legeonaf/robotics.ellak/images/iHome.jpg

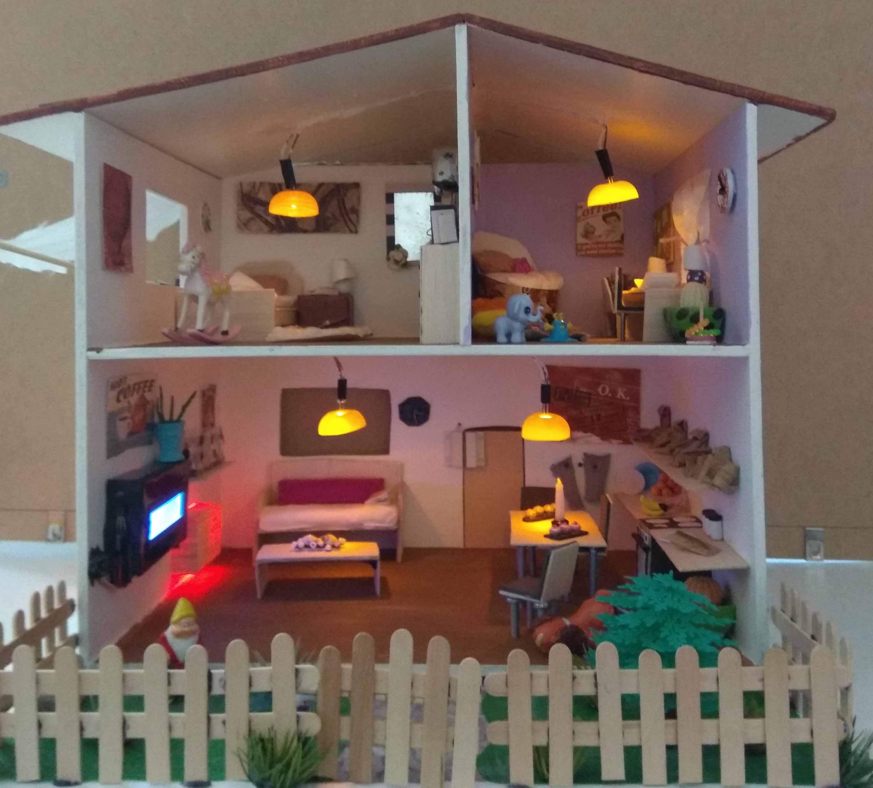
images/iHome.jpg
