legeonaf/robotics.ellak/photos/_MG_0073_resize.jpg

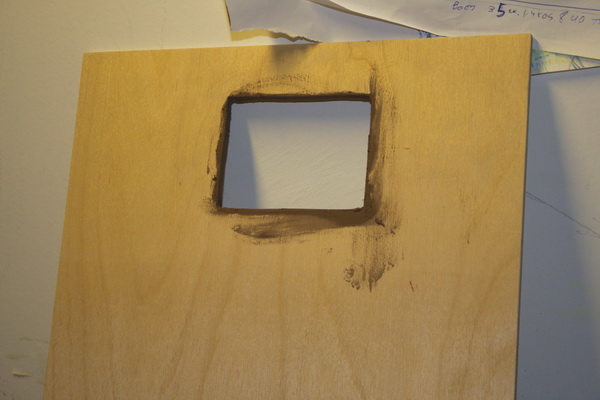
photos/_MG_0073_resize.jpg
