legeonaf/robotics.ellak/photos/_MG_0074_resize.jpg

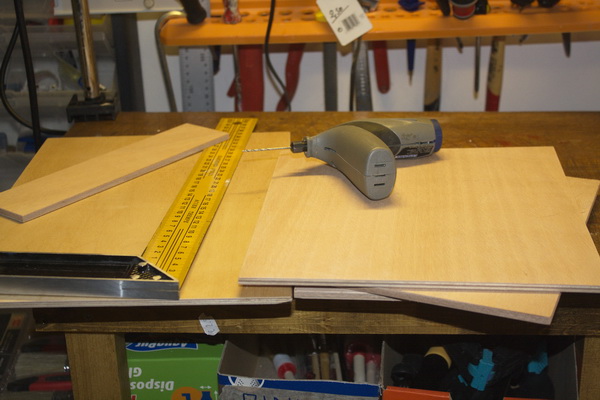
photos/_MG_0074_resize.jpg
