legeonaf/robotics.ellak/photos/_MG_0078_resize.jpg

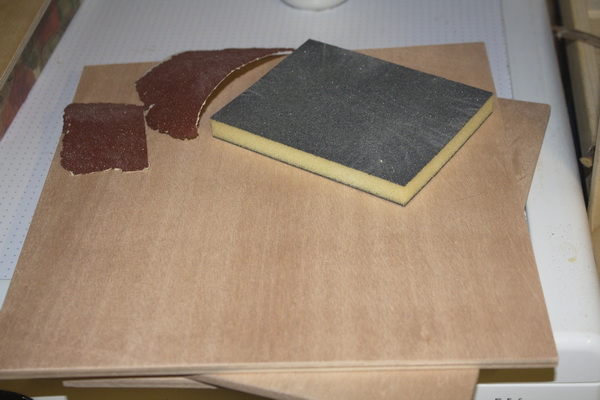
photos/_MG_0078_resize.jpg
