legeonaf/robotics.ellak/photos/_MG_0083_resize.jpg

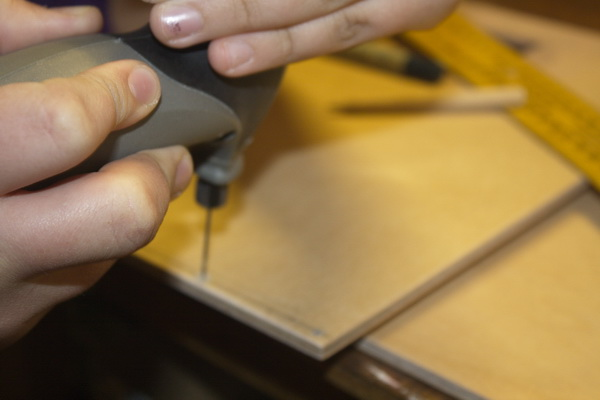
photos/_MG_0083_resize.jpg
