legeonaf/robotics.ellak/photos/_MG_0085_resize.jpg

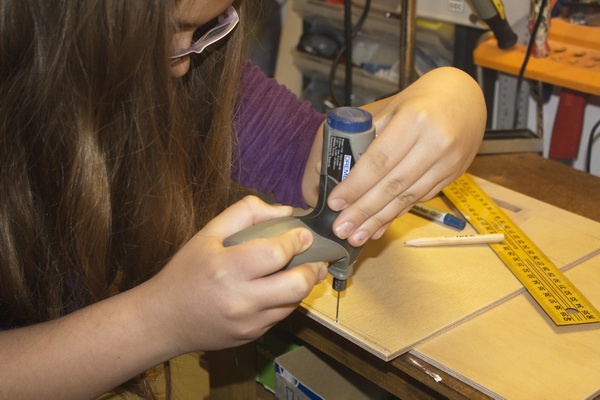
photos/_MG_0085_resize.jpg
