legeonaf/robotics.ellak/photos/_MG_0087_resize.jpg

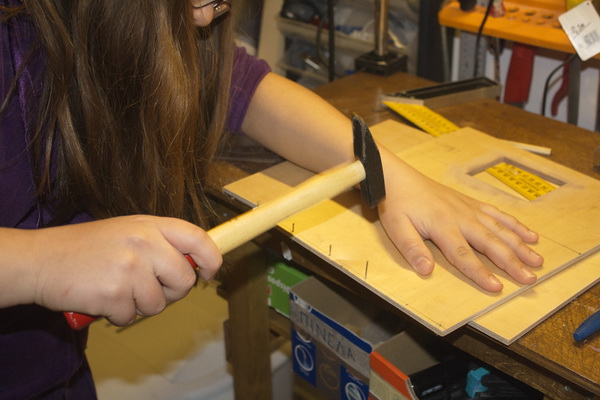
photos/_MG_0087_resize.jpg
