legeonaf/robotics.ellak/photos/_MG_0088_resize.jpg

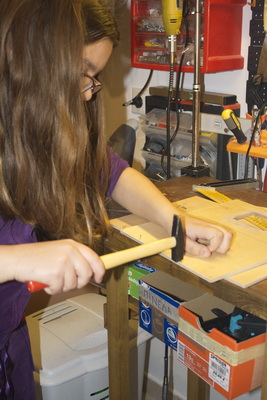
photos/_MG_0088_resize.jpg
