legeonaf/robotics.ellak/photos/_MG_0089_resize.jpg

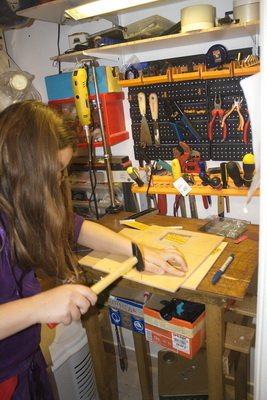
photos/_MG_0089_resize.jpg
