legeonaf/robotics.ellak/photos/_MG_0090_resize.jpg

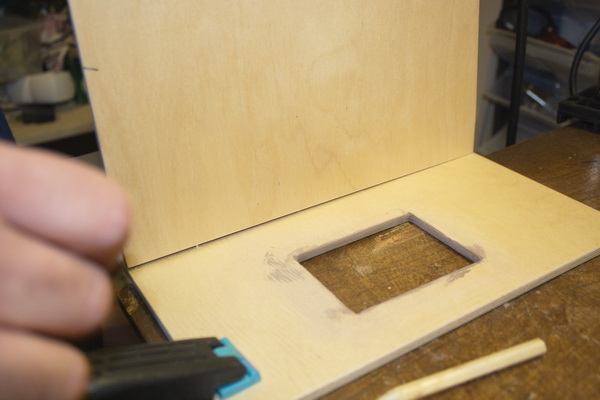
photos/_MG_0090_resize.jpg
