legeonaf/robotics.ellak/photos/_MG_0091_resize.jpg

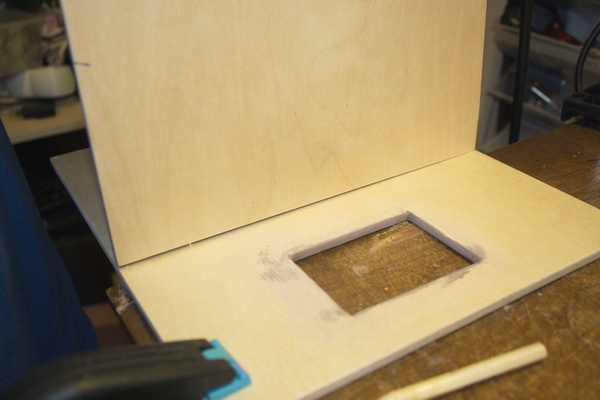
photos/_MG_0091_resize.jpg
