legeonaf/robotics.ellak/photos/_MG_0105_resize.jpg

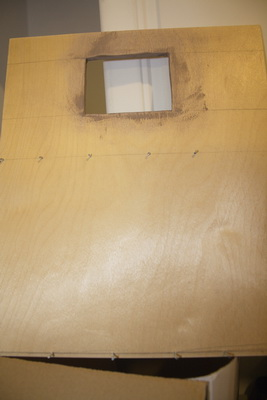
photos/_MG_0105_resize.jpg
