legeonaf/robotics.ellak/photos/_MG_0110_resize.jpg

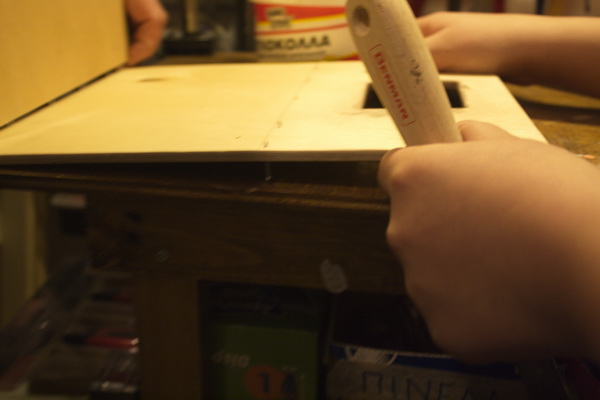
photos/_MG_0110_resize.jpg
