legeonaf/robotics.ellak/photos/_MG_0133_resize.jpg

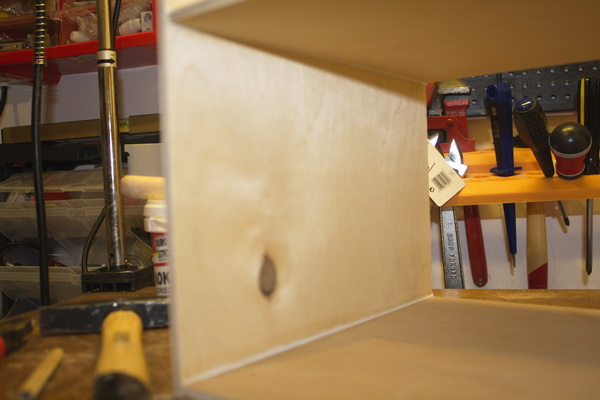
photos/_MG_0133_resize.jpg
