legeonaf/robotics.ellak/photos/_MG_0134_resize.jpg

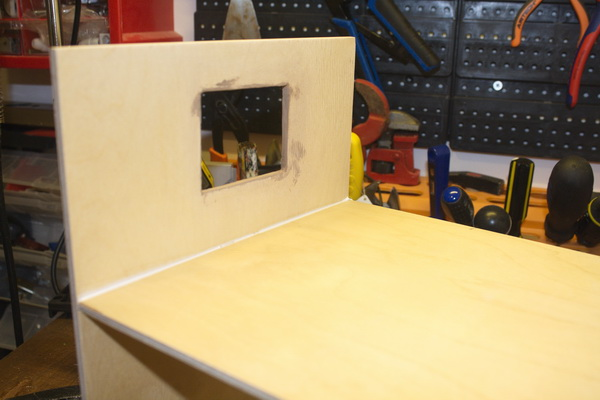
photos/_MG_0134_resize.jpg
