legeonaf/robotics.ellak/photos/_MG_0135_resize.jpg

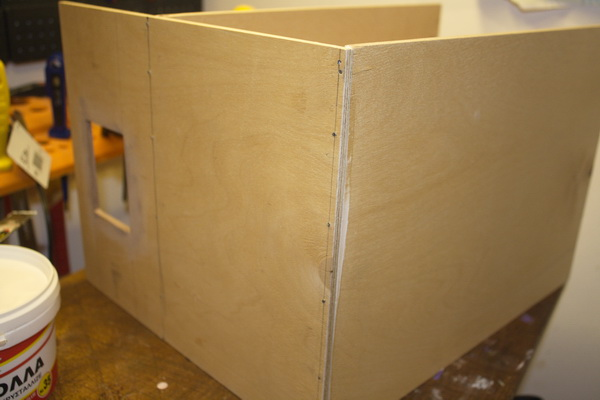
photos/_MG_0135_resize.jpg
