legeonaf/robotics.ellak/photos/_MG_0138_resize.jpg

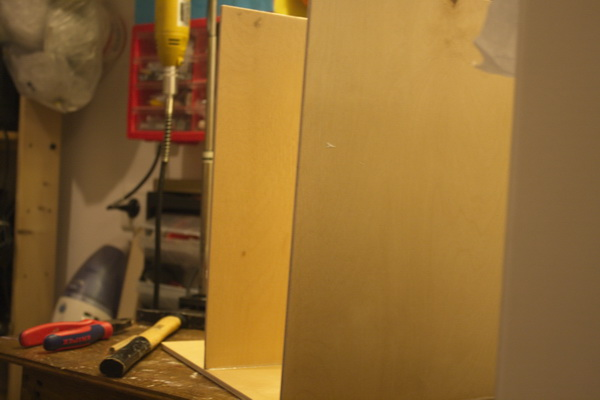
photos/_MG_0138_resize.jpg
