legeonaf/robotics.ellak/photos/_MG_0139_resize.jpg

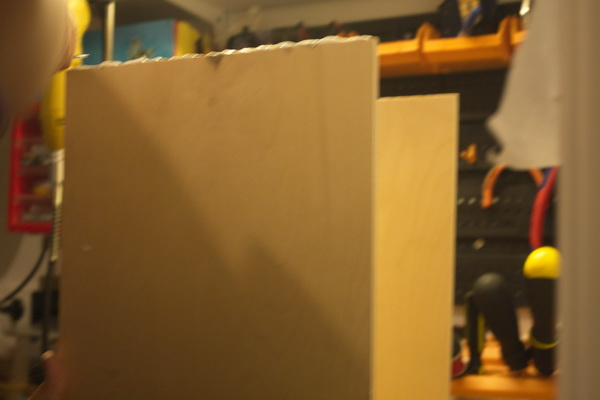
photos/_MG_0139_resize.jpg
