legeonaf/robotics.ellak/photos/_MG_0140_resize.jpg

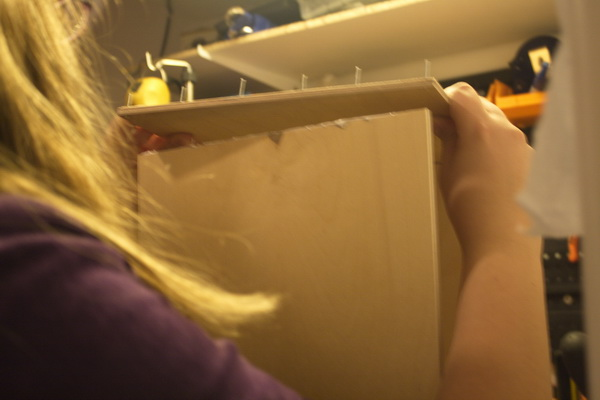
photos/_MG_0140_resize.jpg
