legeonaf/robotics.ellak/photos/_MG_0141_resize.jpg

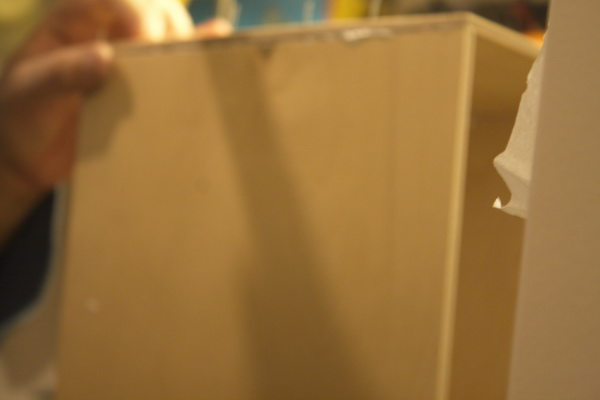
photos/_MG_0141_resize.jpg
