legeonaf/robotics.ellak/photos/_MG_0144_resize.jpg

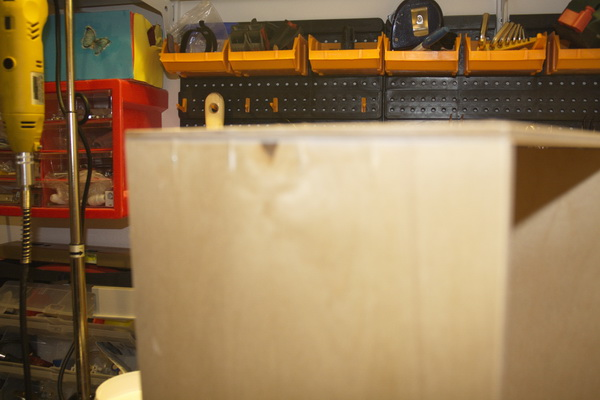
photos/_MG_0144_resize.jpg
