legeonaf/robotics.ellak/photos/_MG_0145_resize.jpg

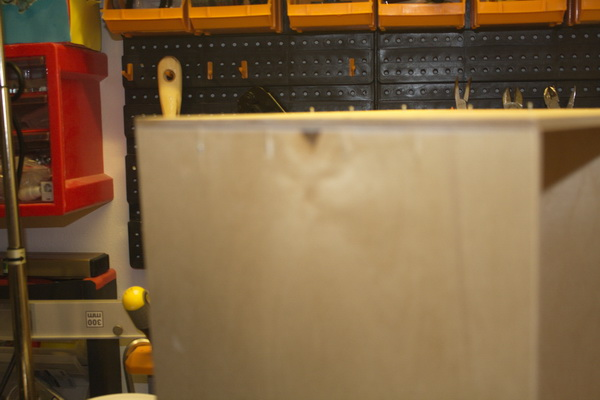
photos/_MG_0145_resize.jpg
