legeonaf/robotics.ellak/photos/_MG_0146_resize.jpg

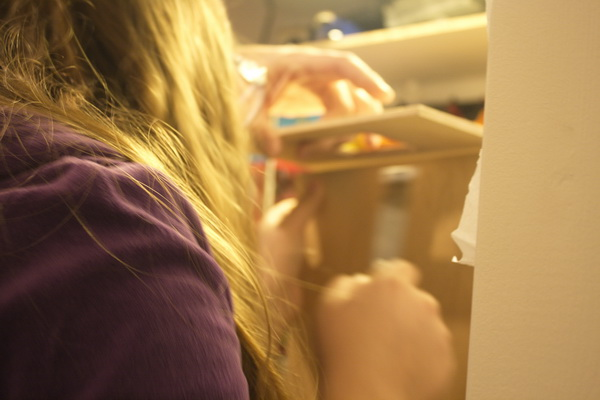
photos/_MG_0146_resize.jpg
