legeonaf/robotics.ellak/photos/_MG_0149_resize.jpg

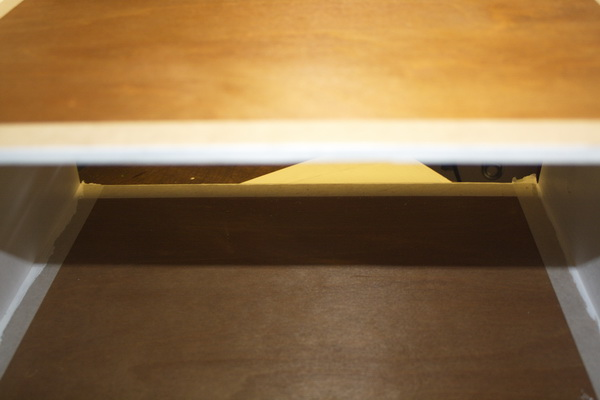
photos/_MG_0149_resize.jpg
