legeonaf/robotics.ellak/photos/_MG_0150_resize.jpg

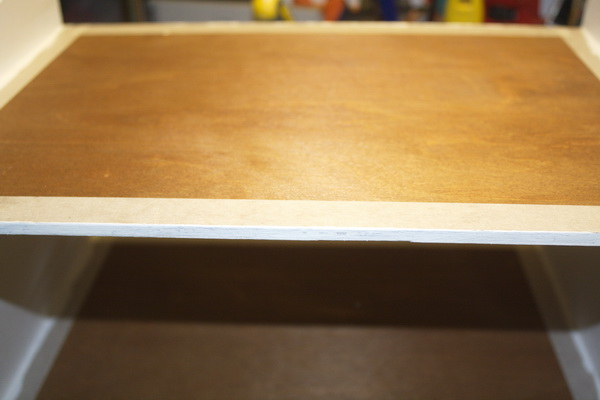
photos/_MG_0150_resize.jpg
