legeonaf/robotics.ellak/photos/_MG_0152_resize.jpg

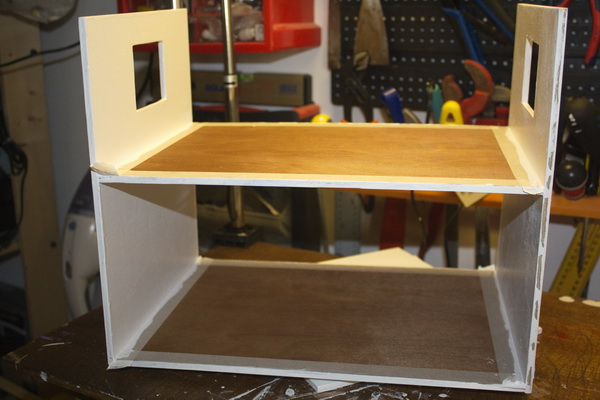
photos/_MG_0152_resize.jpg
