legeonaf/robotics.ellak/photos/_MG_0153_resize.jpg

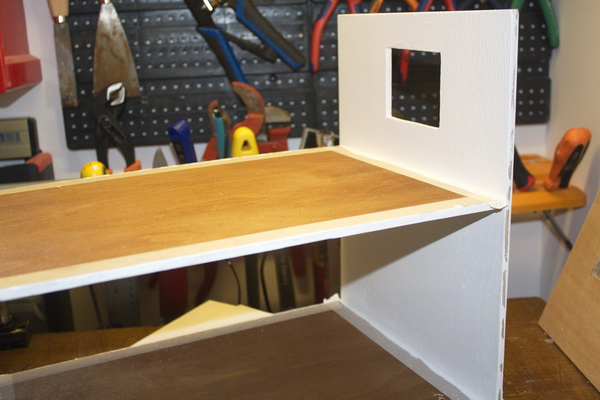
photos/_MG_0153_resize.jpg
