legeonaf/robotics.ellak/photos/_MG_0154_resize.jpg

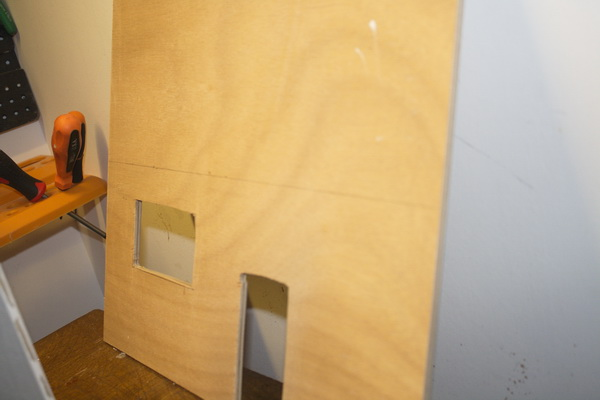
photos/_MG_0154_resize.jpg
