legeonaf/robotics.ellak/photos/_MG_0155_resize.jpg

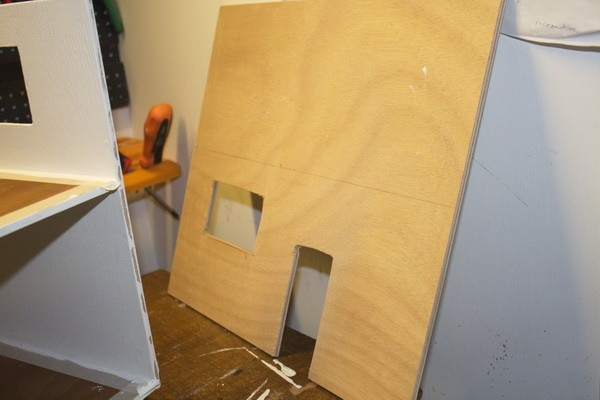
photos/_MG_0155_resize.jpg
