legeonaf/robotics.ellak/photos/_MG_0157_resize.jpg

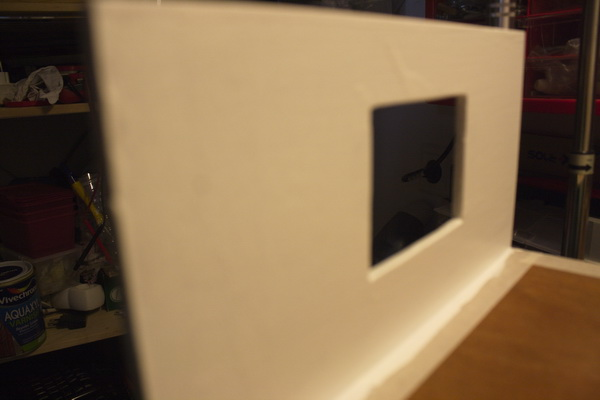
photos/_MG_0157_resize.jpg
