legeonaf/robotics.ellak/photos/_MG_0168_resize.jpg

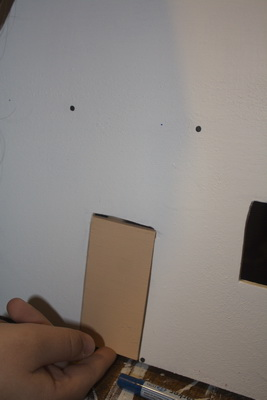
photos/_MG_0168_resize.jpg
