legeonaf/robotics.ellak/photos/_MG_0169_resize.jpg

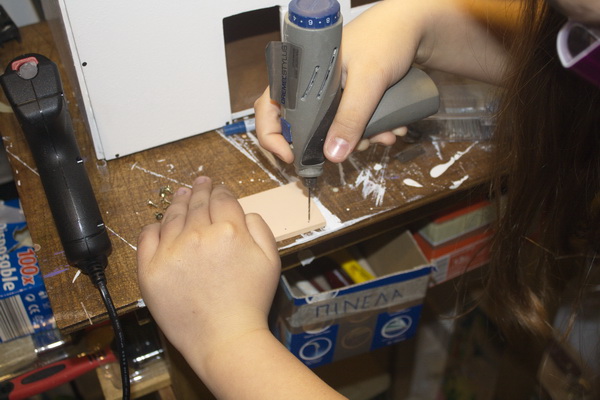
photos/_MG_0169_resize.jpg
