legeonaf/robotics.ellak/photos/_MG_0170_resize.jpg

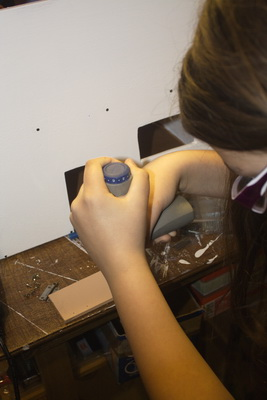
photos/_MG_0170_resize.jpg
