legeonaf/robotics.ellak/photos/_MG_0171_resize.jpg

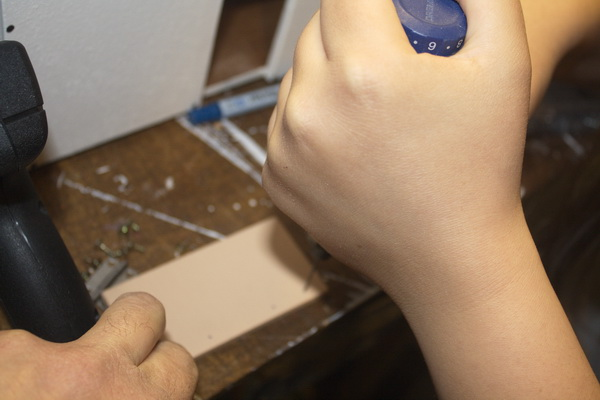
photos/_MG_0171_resize.jpg
