legeonaf/robotics.ellak/photos/_MG_0172_resize.jpg

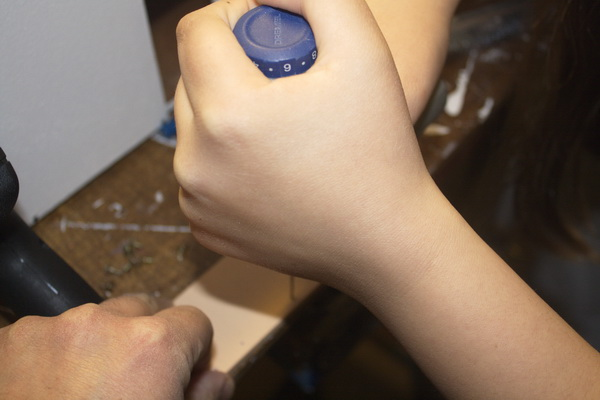
photos/_MG_0172_resize.jpg
