legeonaf/robotics.ellak/photos/_MG_0173_resize.jpg

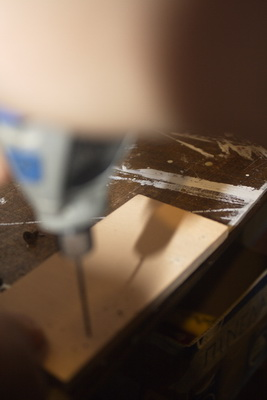
photos/_MG_0173_resize.jpg
