legeonaf/robotics.ellak/photos/_MG_0174_resize.jpg

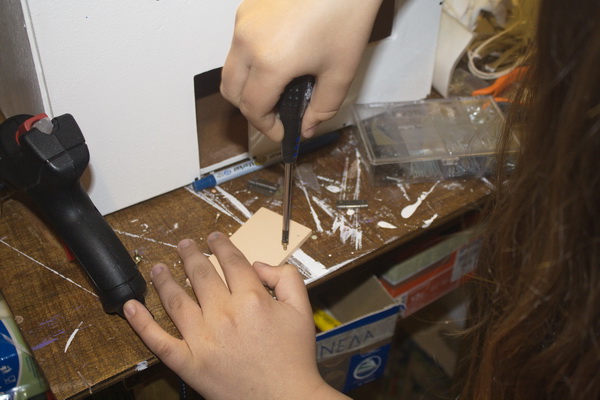
photos/_MG_0174_resize.jpg
