legeonaf/robotics.ellak/photos/_MG_0175_resize.jpg

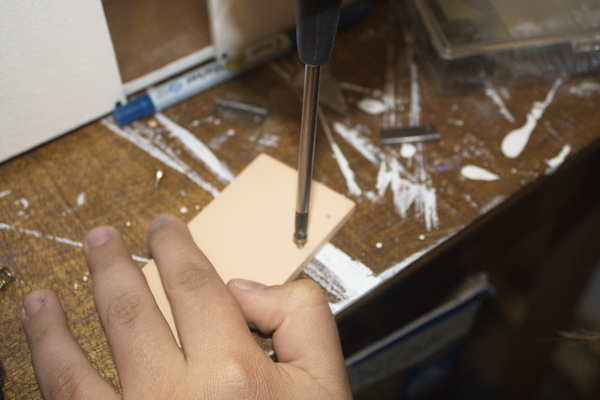
photos/_MG_0175_resize.jpg
