legeonaf/robotics.ellak/photos/_MG_0176_resize.jpg

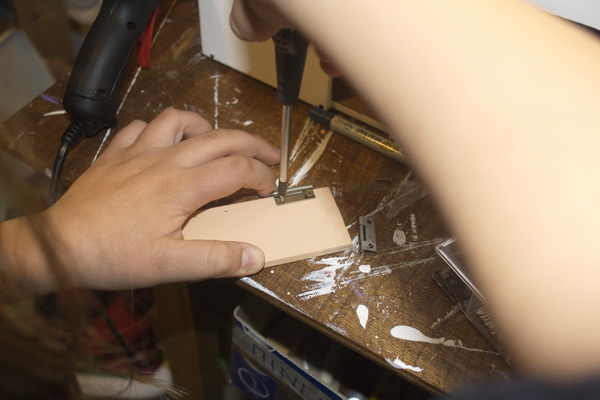
photos/_MG_0176_resize.jpg
