legeonaf/robotics.ellak/photos/_MG_0177_resize.jpg

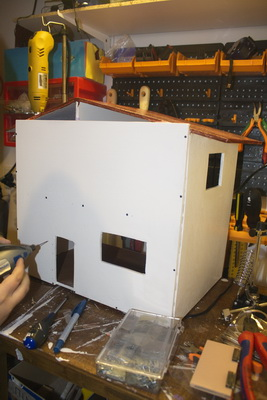
photos/_MG_0177_resize.jpg
