legeonaf/robotics.ellak/photos/_MG_0178_resize.jpg

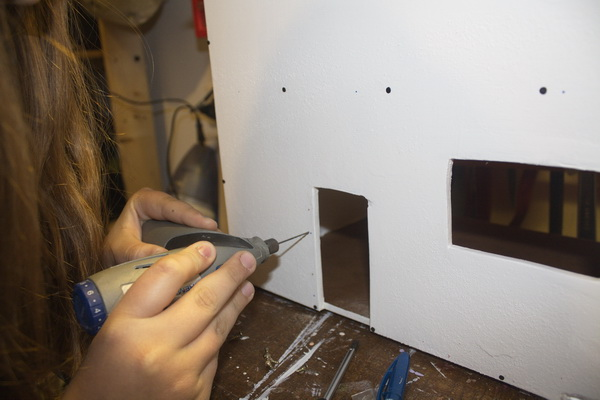
photos/_MG_0178_resize.jpg
