legeonaf/robotics.ellak/photos/_MG_0179_resize.jpg

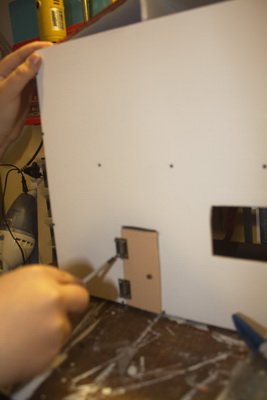
photos/_MG_0179_resize.jpg
