legeonaf/robotics.ellak/photos/_MG_0180_resize.jpg

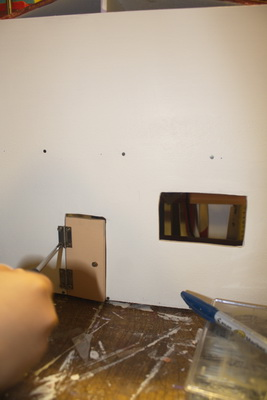
photos/_MG_0180_resize.jpg
