legeonaf/robotics.ellak/photos/_MG_0183_resize.jpg

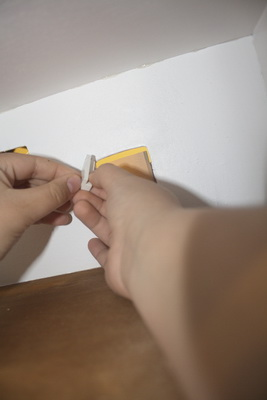
photos/_MG_0183_resize.jpg
