legeonaf/robotics.ellak/photos/_MG_0184_resize.jpg

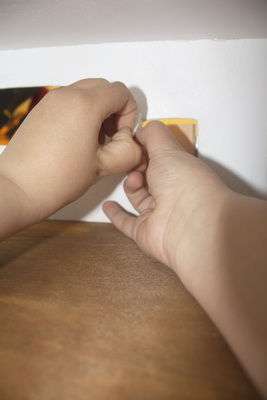
photos/_MG_0184_resize.jpg
