legeonaf/robotics.ellak/photos/_MG_0185_resize.jpg

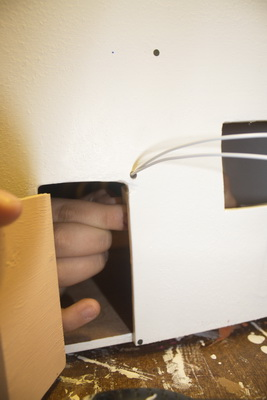
photos/_MG_0185_resize.jpg
