legeonaf/robotics.ellak/photos/_MG_0186_resize.jpg

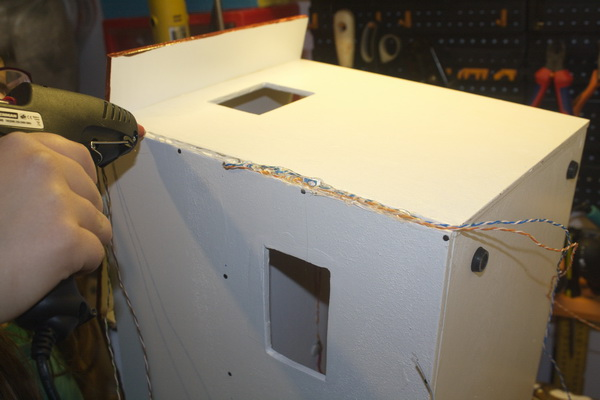
photos/_MG_0186_resize.jpg
