legeonaf/robotics.ellak/photos/_MG_0187_resize.jpg

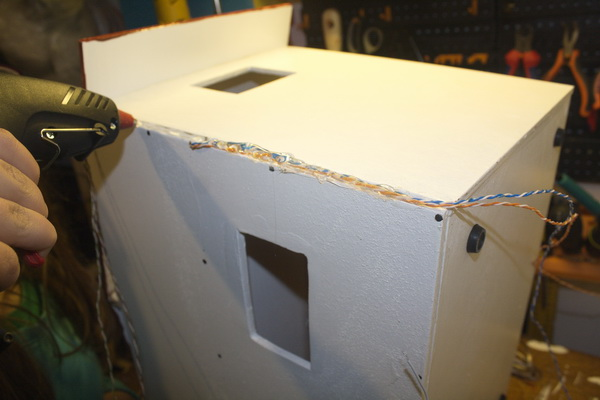
photos/_MG_0187_resize.jpg
