legeonaf/robotics.ellak/photos/IMG_0162_resize.JPG

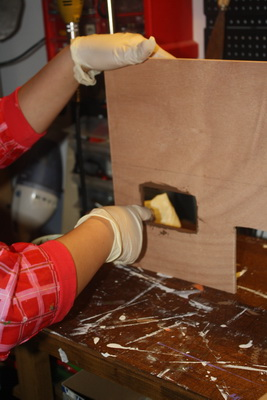
photos/IMG_0162_resize.JPG
