legeonaf/robotics.ellak/photos/IMG_0163_resize.JPG

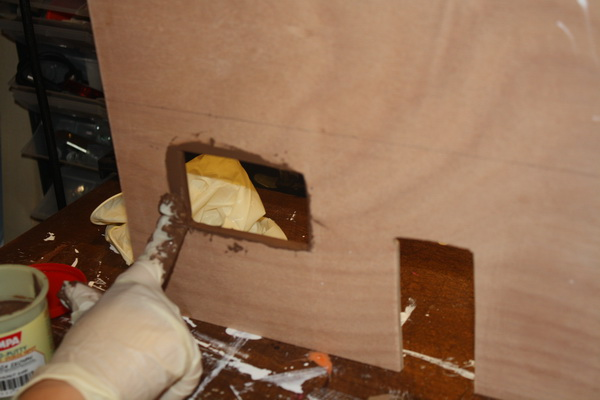
photos/IMG_0163_resize.JPG
