legeonaf/robotics.ellak/photos/IMG_0258_resize.JPG

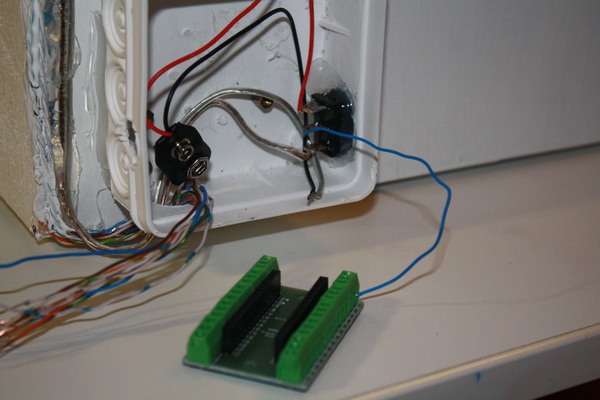
photos/IMG_0258_resize.JPG
