legeonaf/robotics.ellak/photos/IMG_0259_resize.JPG

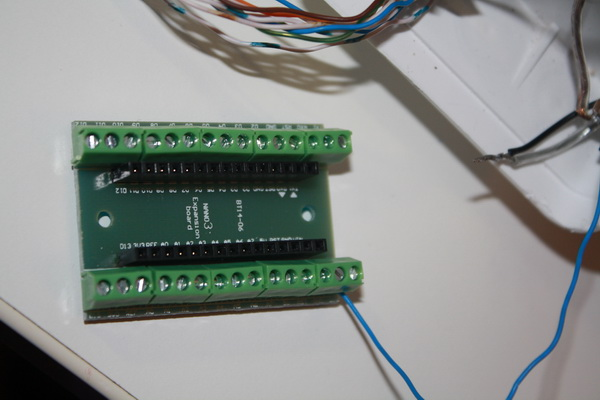
photos/IMG_0259_resize.JPG
