legeonaf/robotics.ellak/photos/IMG_0260_resize.JPG

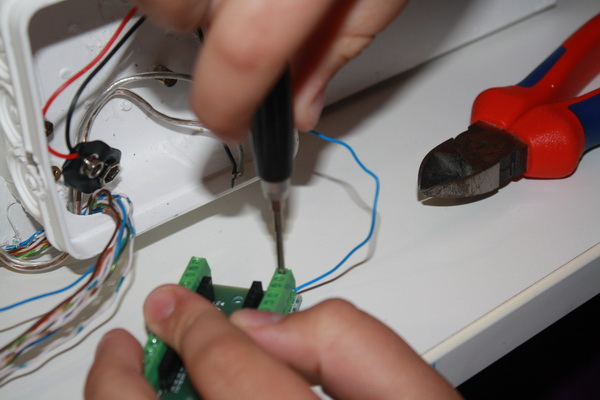
photos/IMG_0260_resize.JPG
