legeonaf/robotics.ellak/photos/IMG_0262_resize.JPG

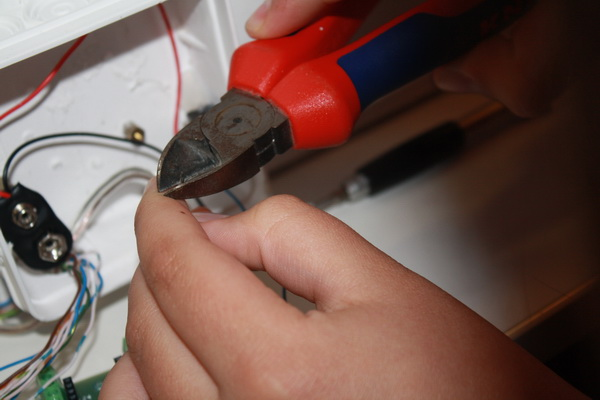
photos/IMG_0262_resize.JPG
