legeonaf/robotics.ellak/photos/IMG_0263_resize.JPG

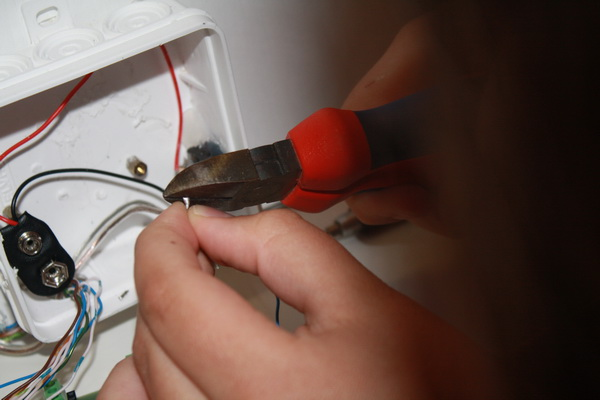
photos/IMG_0263_resize.JPG
