legeonaf/robotics.ellak/photos/IMG_0264_resize.JPG

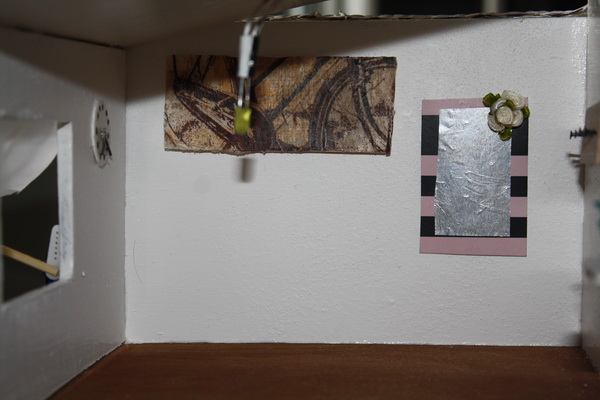
photos/IMG_0264_resize.JPG
