legeonaf/robotics.ellak/photos/IMG_0265_resize.JPG

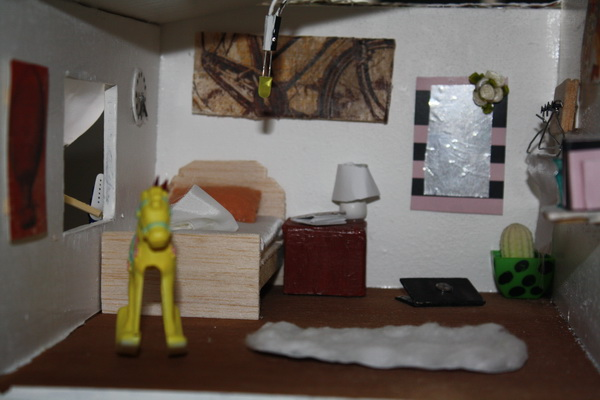
photos/IMG_0265_resize.JPG
