legeonaf/robotics.ellak/photos/IMG_0266_resize.JPG

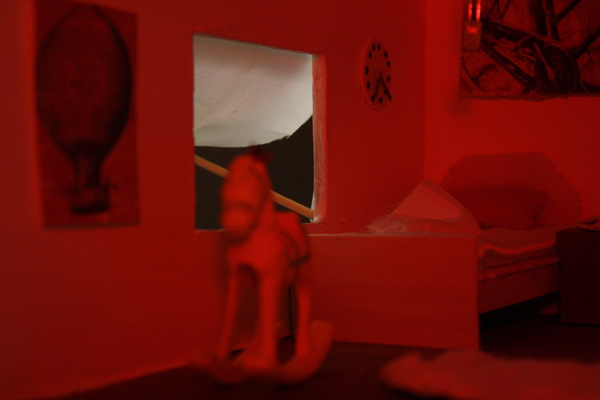
photos/IMG_0266_resize.JPG
