legeonaf/robotics.ellak/photos/IMG_0267_resize.JPG

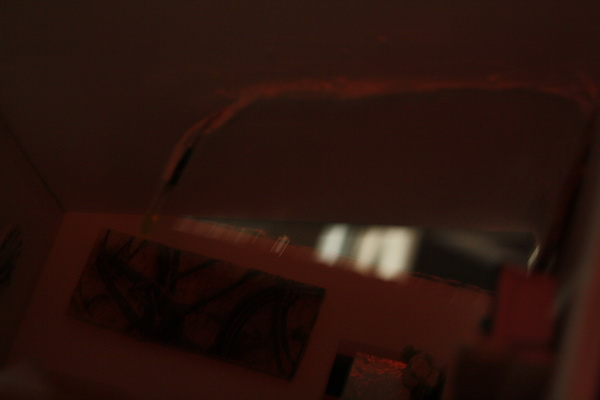
photos/IMG_0267_resize.JPG
