legeonaf/robotics.ellak/photos/IMG_0268_resize.JPG

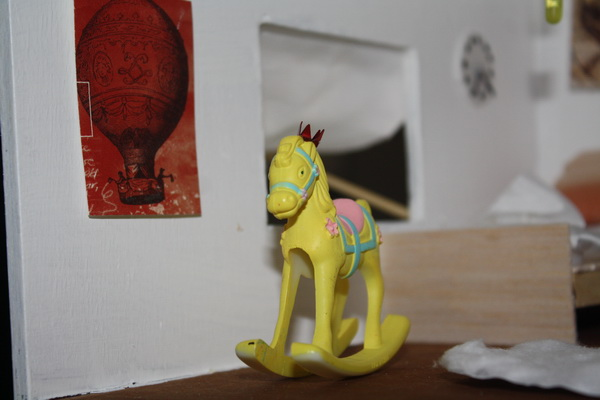
photos/IMG_0268_resize.JPG
