legeonaf/robotics.ellak/photos/IMG_0269_resize.JPG

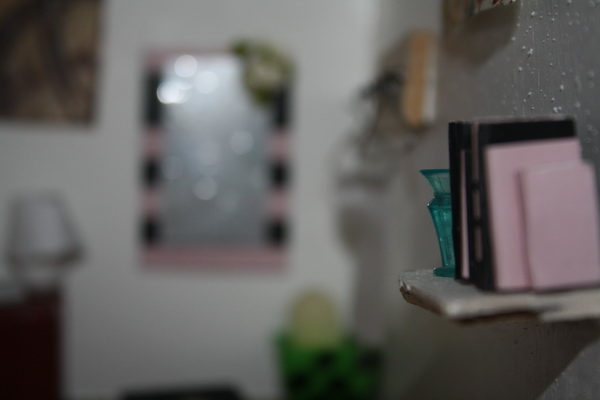
photos/IMG_0269_resize.JPG
