legeonaf/robotics.ellak/photos/IMG_0270_resize.JPG

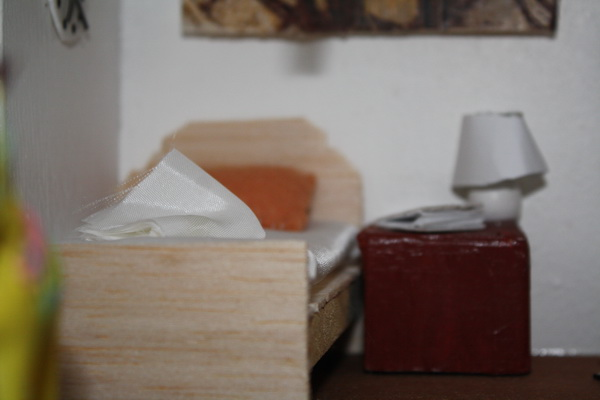
photos/IMG_0270_resize.JPG
