legeonaf/robotics.ellak/photos/IMG_0271_resize.JPG

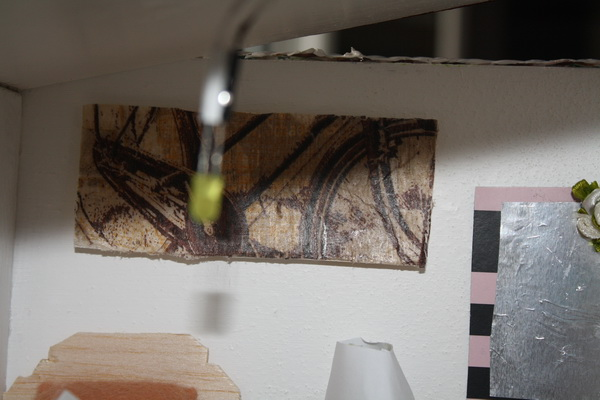
photos/IMG_0271_resize.JPG
