legeonaf/robotics.ellak/photos/IMG_0272_resize.JPG

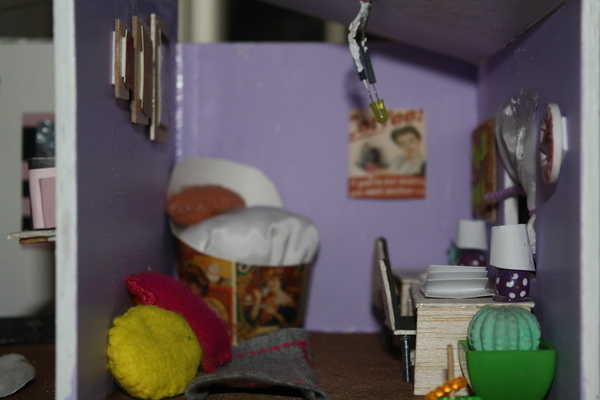
photos/IMG_0272_resize.JPG
