legeonaf/robotics.ellak/photos/IMG_0273_resize.JPG

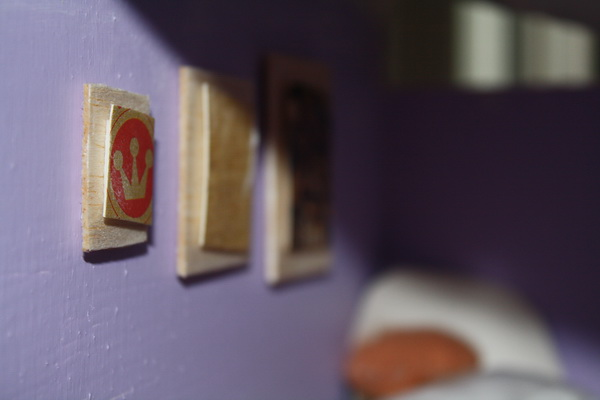
photos/IMG_0273_resize.JPG
