legeonaf/robotics.ellak/photos/IMG_0274_resize.JPG

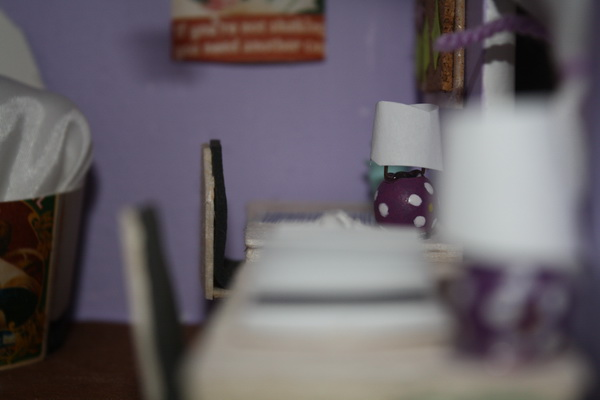
photos/IMG_0274_resize.JPG
