legeonaf/robotics.ellak/photos/IMG_0275_resize.JPG

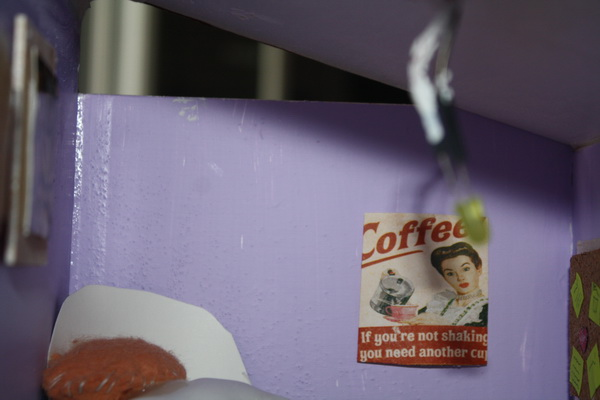
photos/IMG_0275_resize.JPG
