legeonaf/robotics.ellak/photos/IMG_0276_resize.JPG

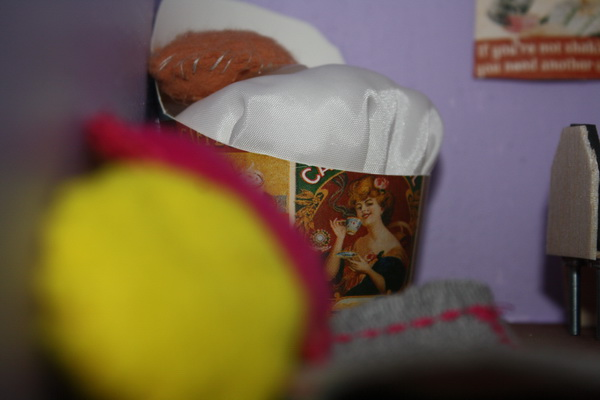
photos/IMG_0276_resize.JPG
