legeonaf/robotics.ellak/photos/IMG_0277_resize.JPG

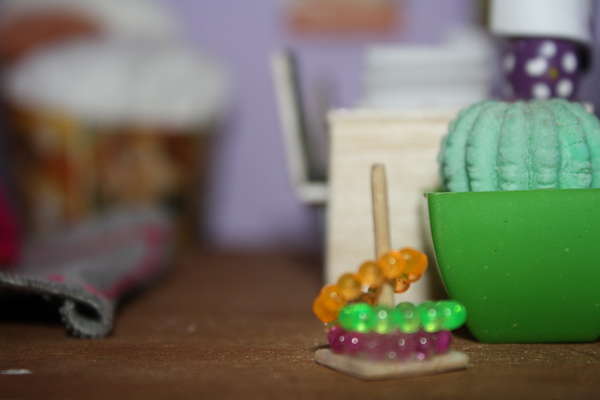
photos/IMG_0277_resize.JPG
