legeonaf/robotics.ellak/photos/IMG_0278_resize.JPG

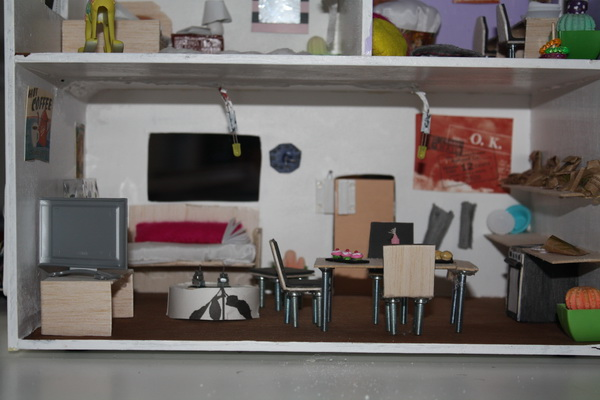
photos/IMG_0278_resize.JPG
