legeonaf/robotics.ellak/photos/IMG_0280_resize.JPG

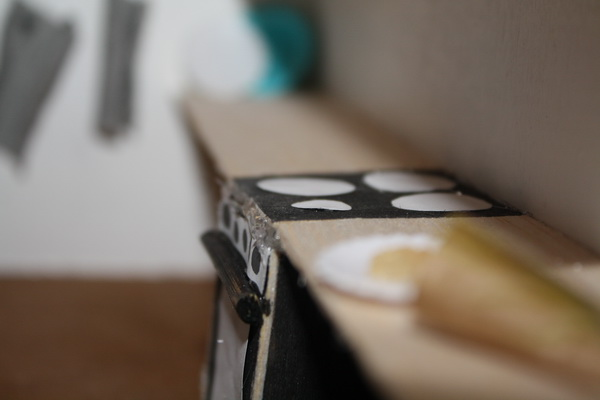
photos/IMG_0280_resize.JPG
