legeonaf/robotics.ellak/photos/IMG_0281_resize.JPG

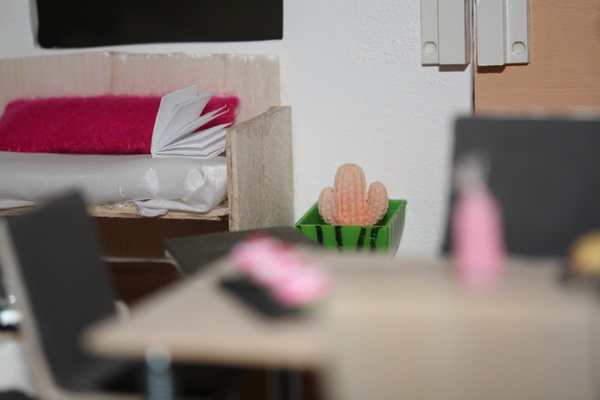
photos/IMG_0281_resize.JPG
