legeonaf/robotics.ellak/photos/IMG_0282_resize.JPG

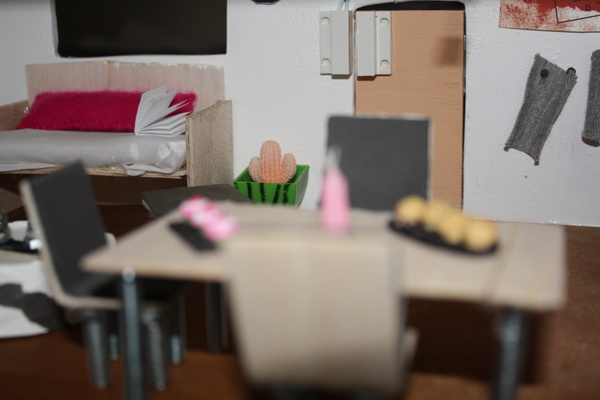
photos/IMG_0282_resize.JPG
