legeonaf/robotics.ellak/photos/IMG_0283_resize.JPG

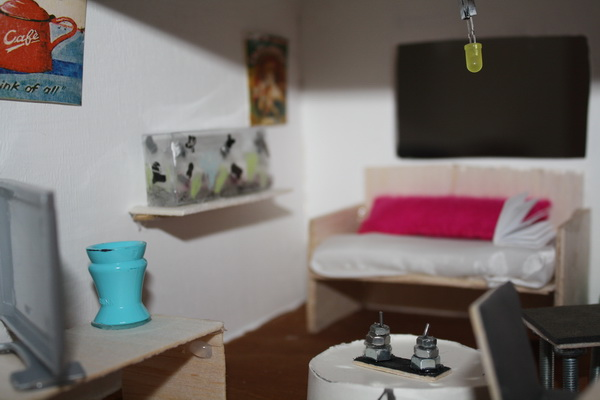
photos/IMG_0283_resize.JPG
