legeonaf/robotics.ellak/photos/IMG_0284_resize.JPG

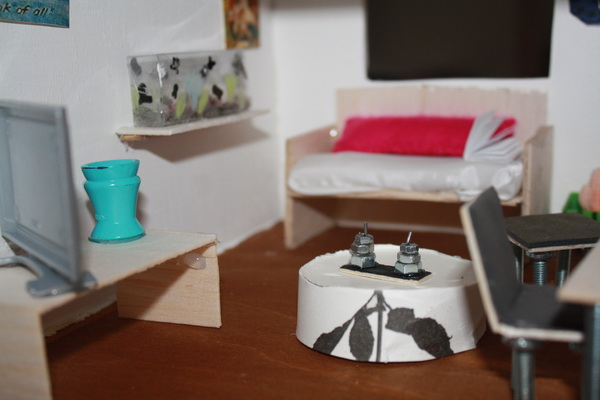
photos/IMG_0284_resize.JPG
