legeonaf/robotics.ellak/photos/IMG_0285_resize.JPG

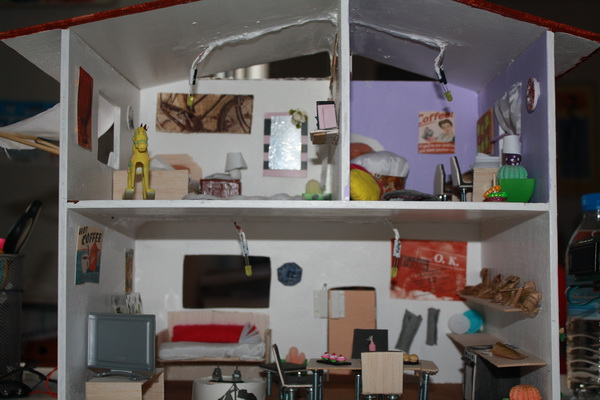
photos/IMG_0285_resize.JPG
