legeonaf/robotics.ellak/photos/IMG_0286_resize.JPG

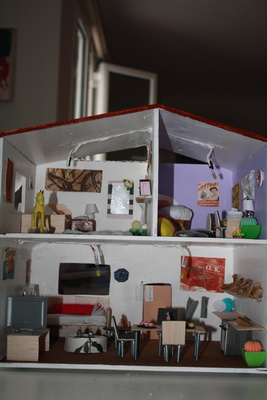
photos/IMG_0286_resize.JPG
