legeonaf/robotics.ellak/photos/IMG_0287_resize.JPG

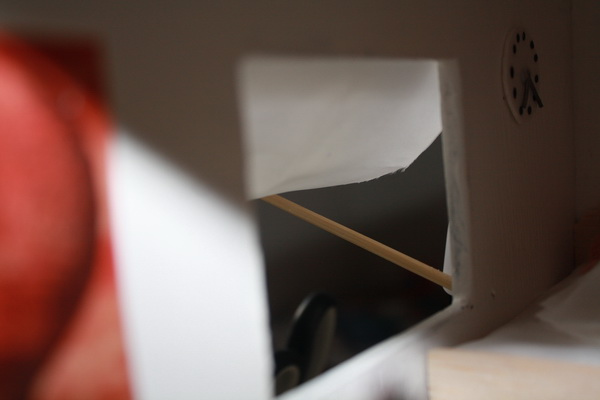
photos/IMG_0287_resize.JPG
