legeonaf/robotics.ellak/photos/IMG_0288_resize.JPG

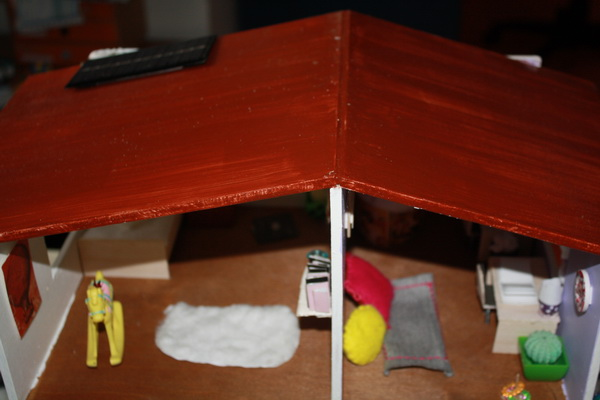
photos/IMG_0288_resize.JPG
