legeonaf/robotics.ellak/photos/IMG_0290_resize.JPG

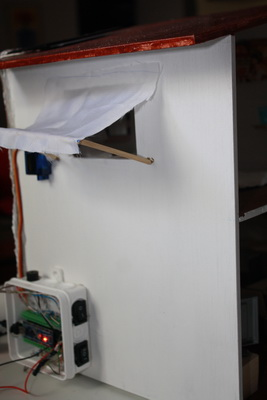
photos/IMG_0290_resize.JPG
