legeonaf/robotics.ellak/photos/IMG_0291_resize.JPG

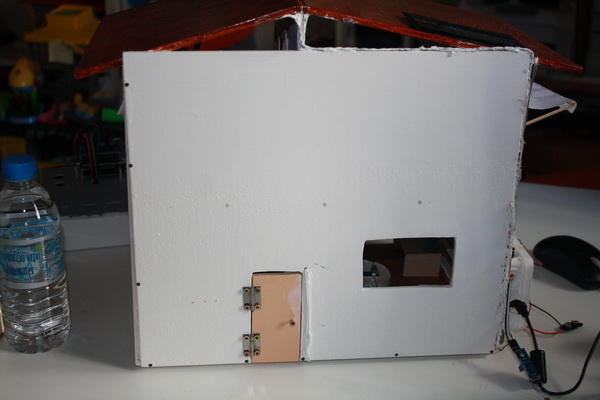
photos/IMG_0291_resize.JPG
