legeonaf/robotics.ellak/photos/IMG_0292_resize.JPG

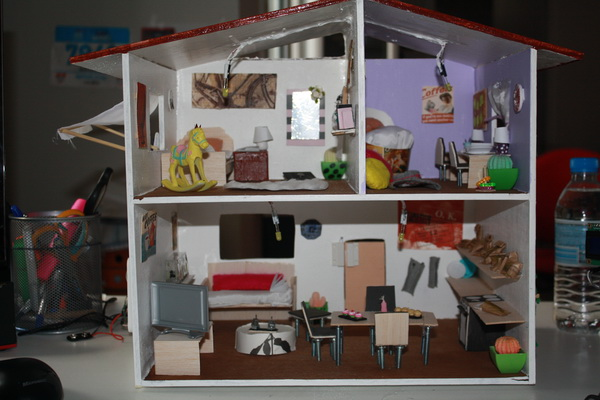
photos/IMG_0292_resize.JPG
