legeonaf/robotics.ellak/photos/IMG_0293_resize.JPG

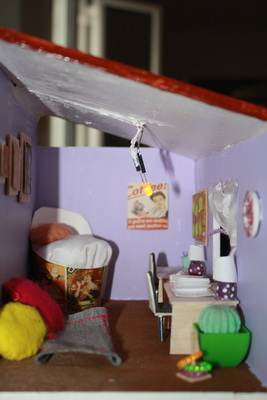
photos/IMG_0293_resize.JPG
