legeonaf/robotics.ellak/photos/IMG_0297_resize.JPG

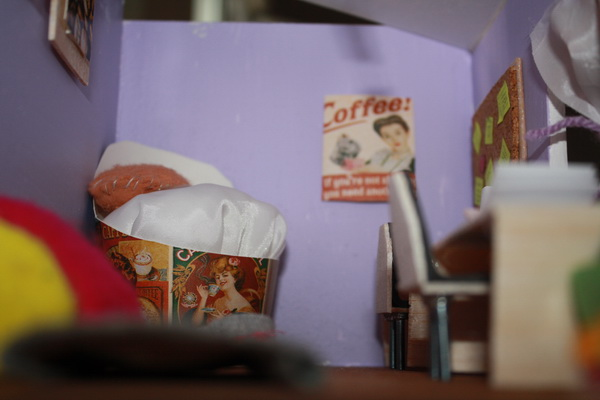
photos/IMG_0297_resize.JPG
