legeonaf/robotics.ellak/photos/IMG_0298_resize.JPG

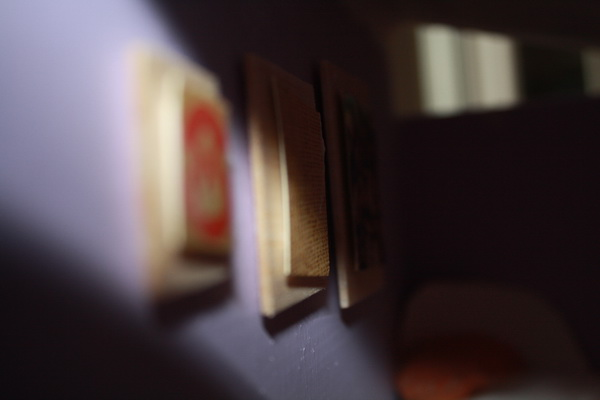
photos/IMG_0298_resize.JPG
