legeonaf/robotics.ellak/photos/IMG_0299_resize.JPG

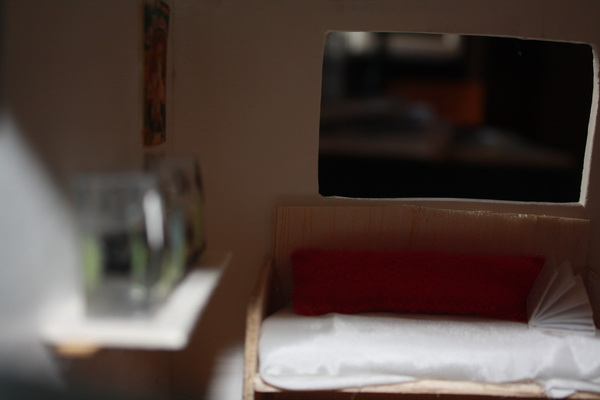
photos/IMG_0299_resize.JPG
