legeonaf/robotics.ellak/photos/IMG_0300_resize.JPG

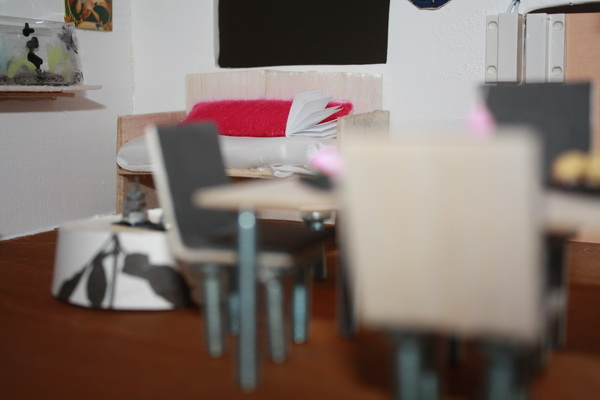
photos/IMG_0300_resize.JPG
