legeonaf/robotics.ellak/photos/IMG_0301_resize.JPG

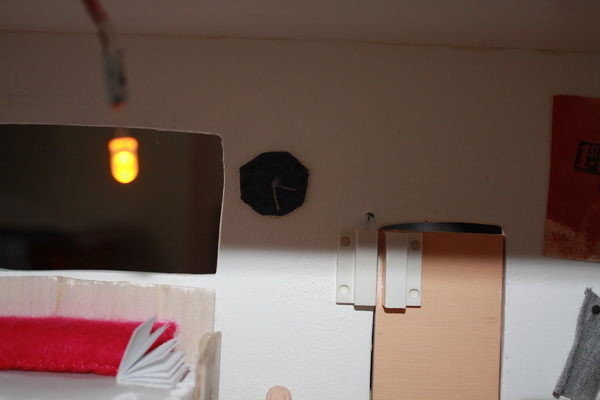
photos/IMG_0301_resize.JPG
