legeonaf/robotics.ellak/photos/IMG_0302_resize.JPG

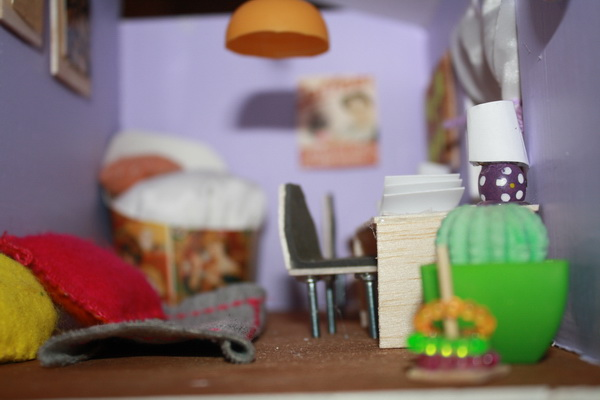
photos/IMG_0302_resize.JPG
