legeonaf/robotics.ellak/photos/IMG_0303_resize.JPG

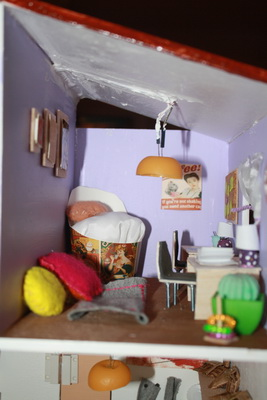
photos/IMG_0303_resize.JPG
