legeonaf/robotics.ellak/photos/IMG_0304_resize.JPG

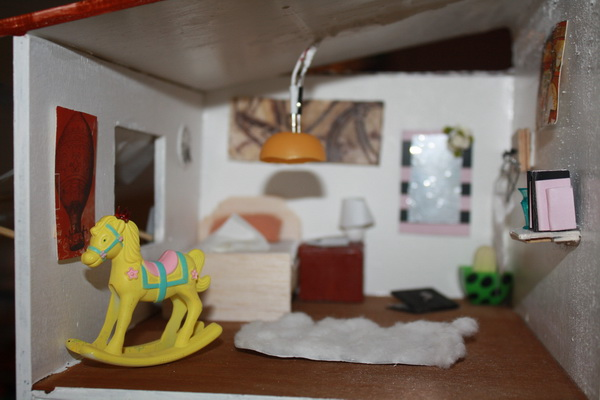
photos/IMG_0304_resize.JPG
