legeonaf/robotics.ellak/photos/IMG_0305_resize.JPG

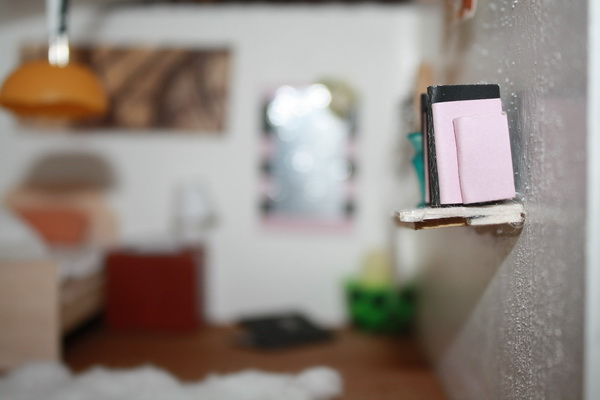
photos/IMG_0305_resize.JPG
