legeonaf/robotics.ellak/photos/IMG_0306_resize.JPG

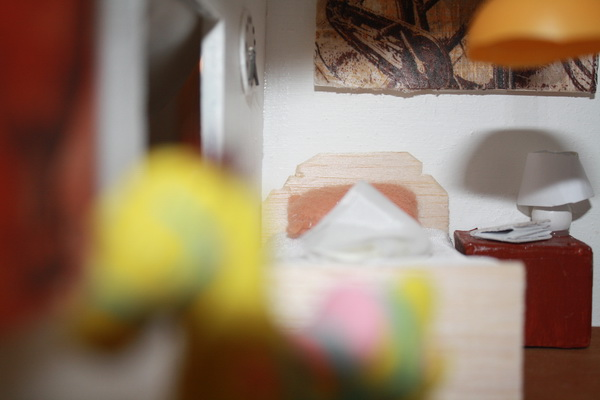
photos/IMG_0306_resize.JPG
