legeonaf/robotics.ellak/photos/IMG_0307_resize.JPG

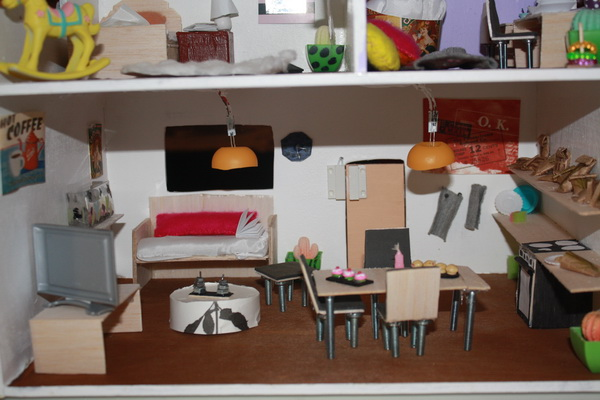
photos/IMG_0307_resize.JPG
