legeonaf/robotics.ellak/photos/IMG_0309_resize.JPG

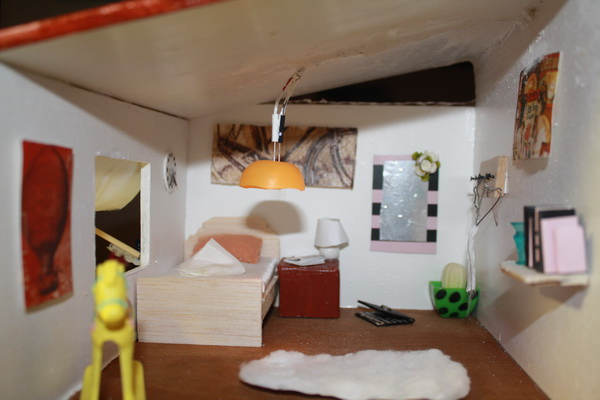
photos/IMG_0309_resize.JPG
