legeonaf/robotics.ellak/photos/IMG_0311_resize.JPG

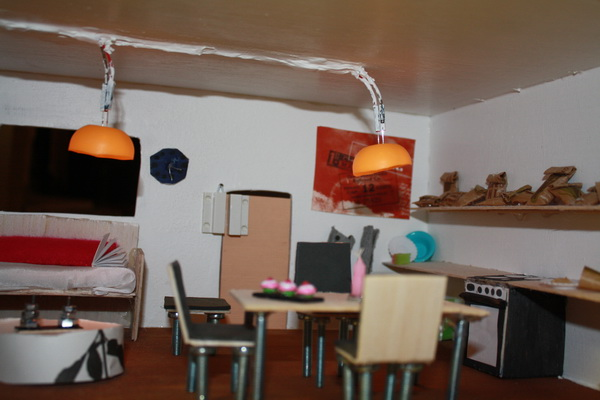
photos/IMG_0311_resize.JPG
