legeonaf/robotics.ellak/photos/IMG_20170331_212338652_resize.jpg

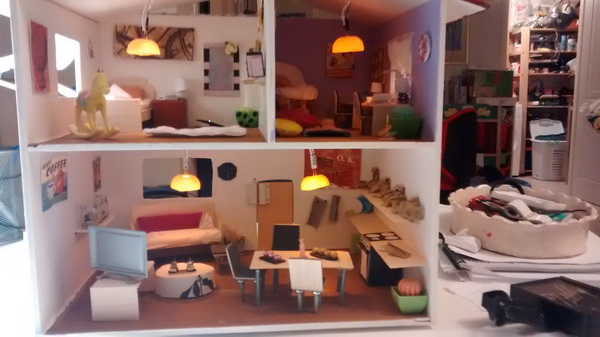
photos/IMG_20170331_212338652_resize.jpg
