legeonaf/robotics.ellak/photos/IMG_20170331_212351922_resize.jpg

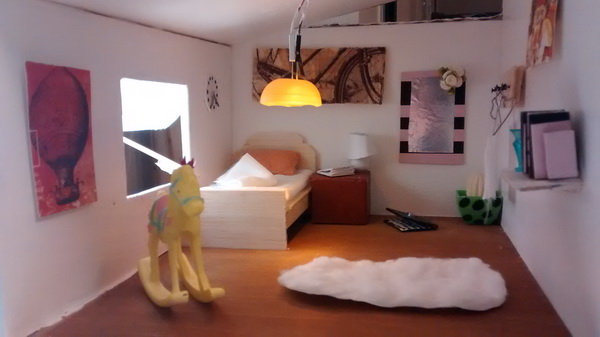
photos/IMG_20170331_212351922_resize.jpg
