legeonaf/robotics.ellak/photos/IMG_20170331_212355842_resize.jpg

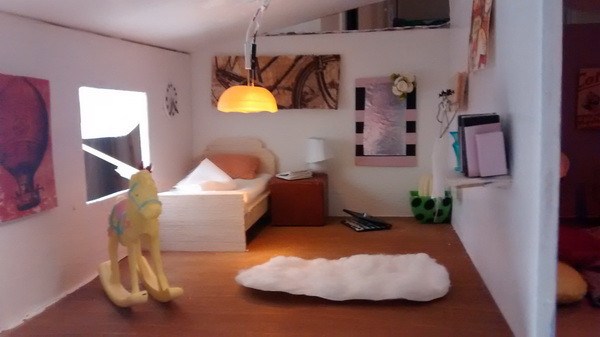
photos/IMG_20170331_212355842_resize.jpg
