legeonaf/robotics.ellak/photos/IMG_20170331_212404386_resize.jpg

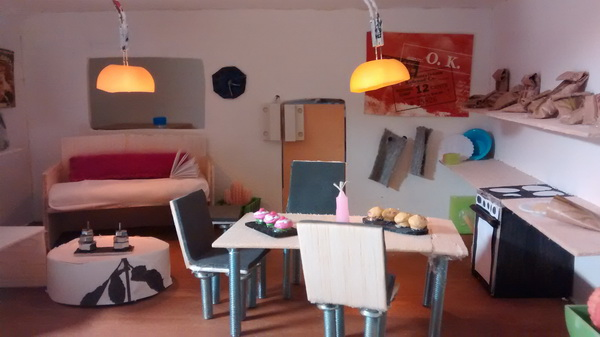
photos/IMG_20170331_212404386_resize.jpg
