legeonaf/robotics.ellak/photos/IMG_20170331_212411022_HDR_resize.jpg

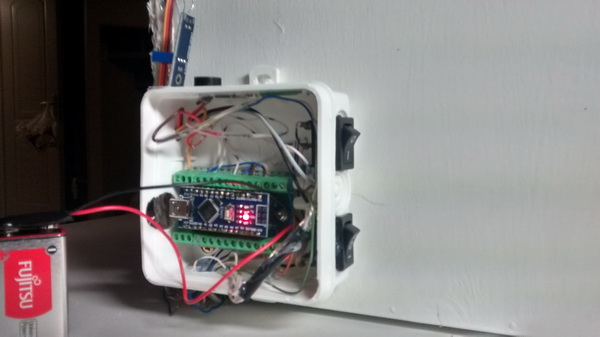
photos/IMG_20170331_212411022_HDR_resize.jpg
