legeonaf/robotics.ellak/photos/IMG_20170331_212437704_HDR_resize.jpg

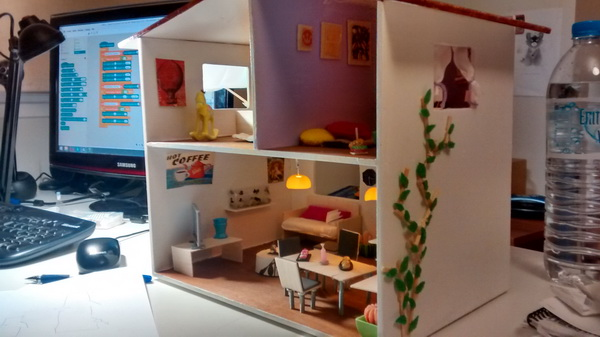
photos/IMG_20170331_212437704_HDR_resize.jpg
