legeonaf/robotics.ellak/Εξαρτήματα/images/Mantra.png

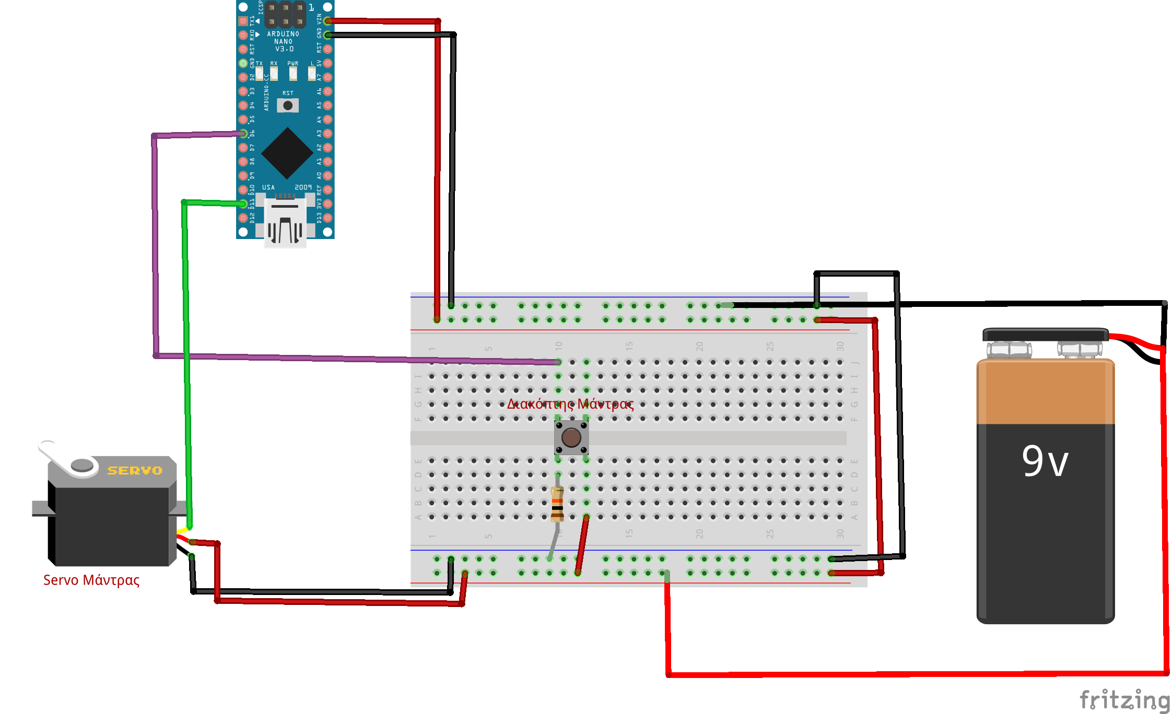
Εξαρτήματα/images/Mantra.png
