legeonaf/robotics.ellak/Εξαρτήματα/images/switch.png

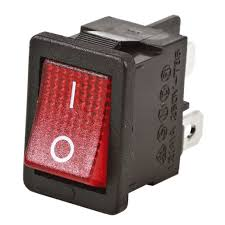
Εξαρτήματα/images/switch.png
